a-bettilyon/pixel-pet/hardware/images/VirtualPetBoardPCBBCu.png

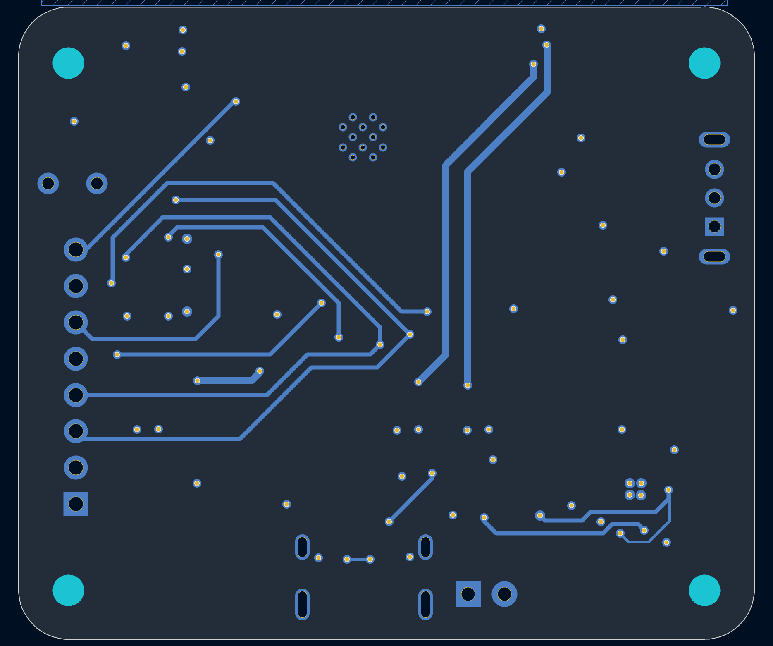
hardware/images/VirtualPetBoardPCBBCu.png
