a-bettilyon/pixel-pet/firmware/buttons.h

#pragma once

bool readBtnA(unsigned long time, bool b1raw, int delay, int longpres);
bool readBtnB(unsigned long time, bool b2raw, int delay, int longpress);
bool readBtnC(unsigned long time, bool b3raw, int delay, int longpress);
